BTrujillo816/coffee-scale/documentation/assets/HX711 Breakout rev A.png

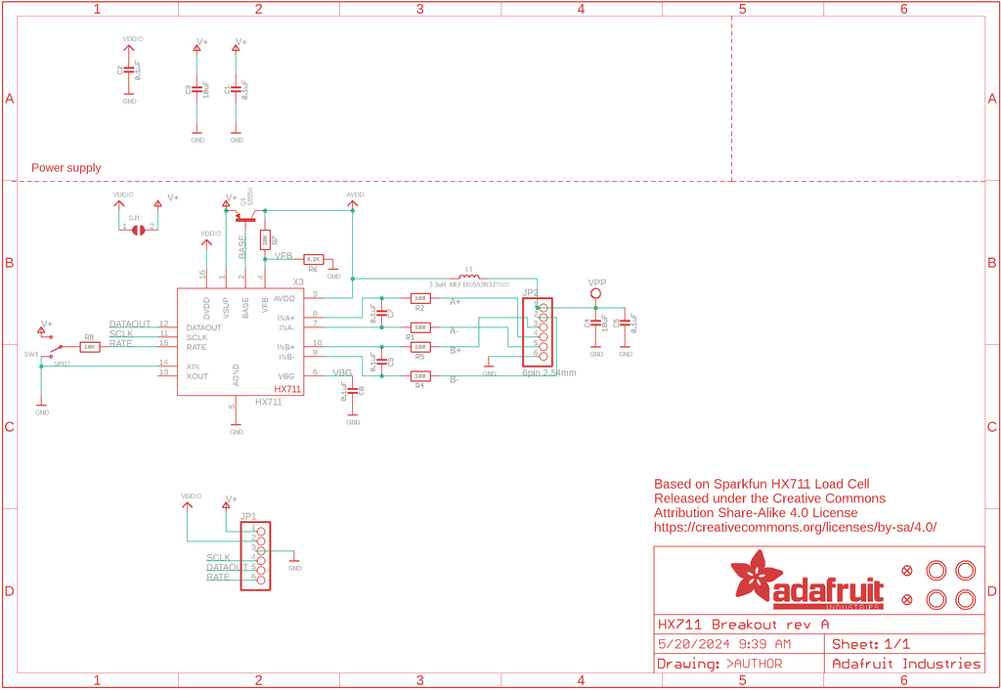
documentation/assets/HX711 Breakout rev A.png
