BTrujillo816/coffee-scale/documentation/TestDocument.assets/Current_prototype_11-13-24.jpg

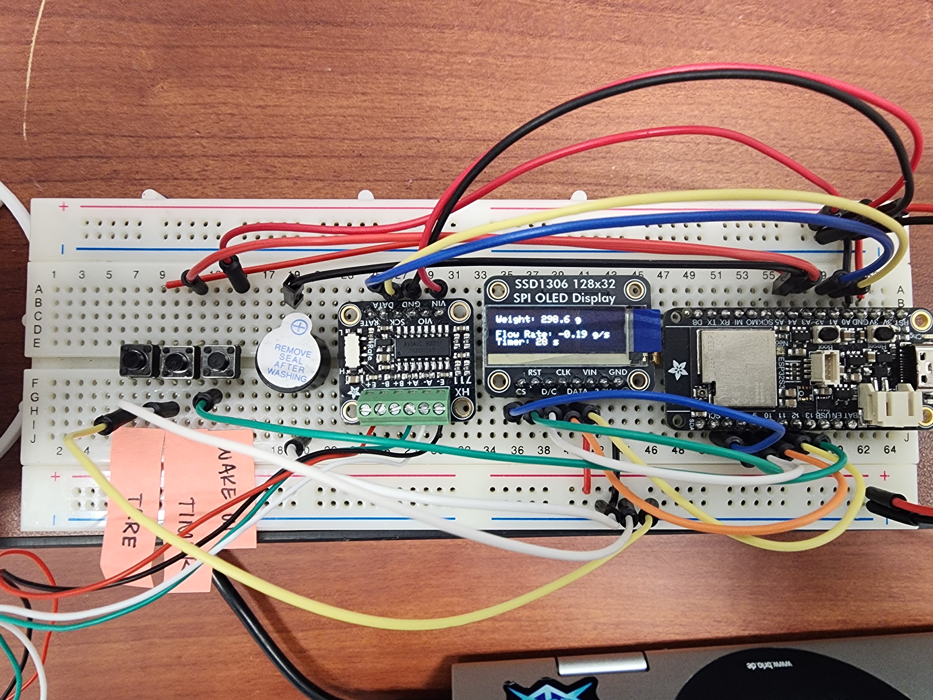
documentation/TestDocument.assets/Current_prototype_11-13-24.jpg
