BTrujillo816/coffee-scale/documentation/TestDocument.assets/Large_weight_test_control.jpg

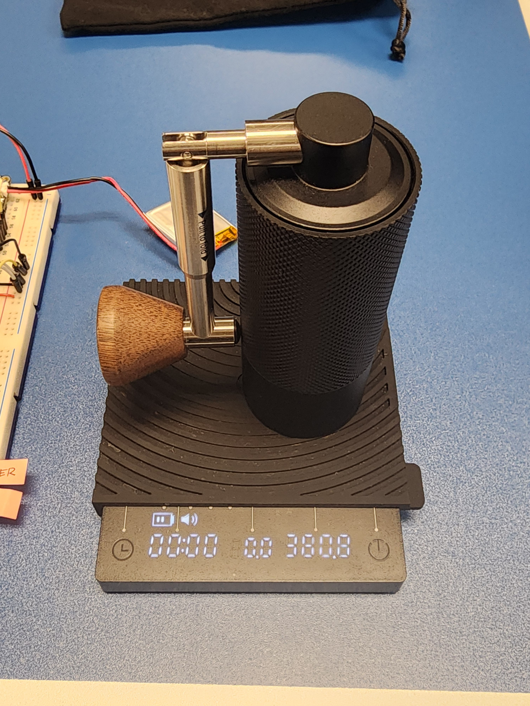
documentation/TestDocument.assets/Large_weight_test_control.jpg
