BTrujillo816/coffee-scale/documentation/Tests-BrandonTrujillo.assets/Types-of-Performance-testing-1024.webp

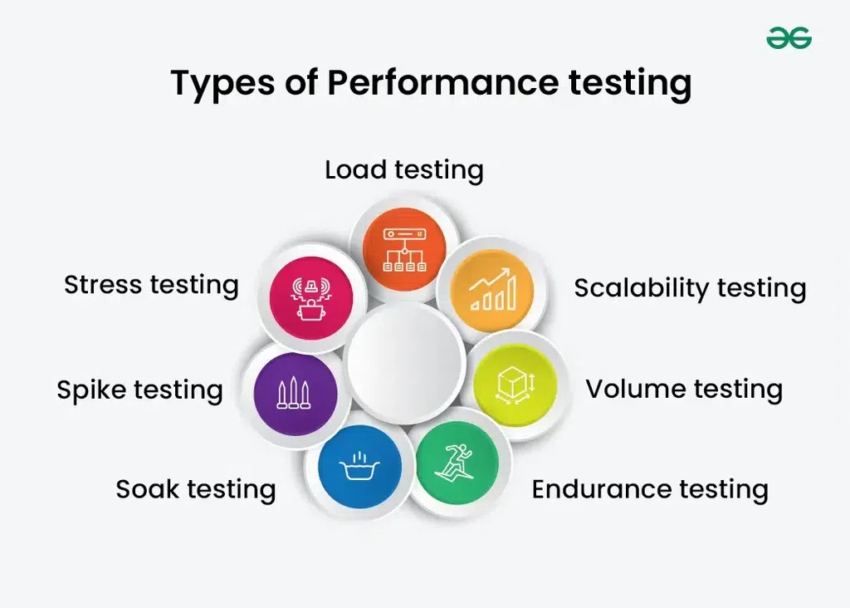
documentation/Tests-BrandonTrujillo.assets/Types-of-Performance-testing-1024.webp
