BTrujillo816/coffee-scale/logbook/10-30-24.assets/Result_LoadCell_Test.png

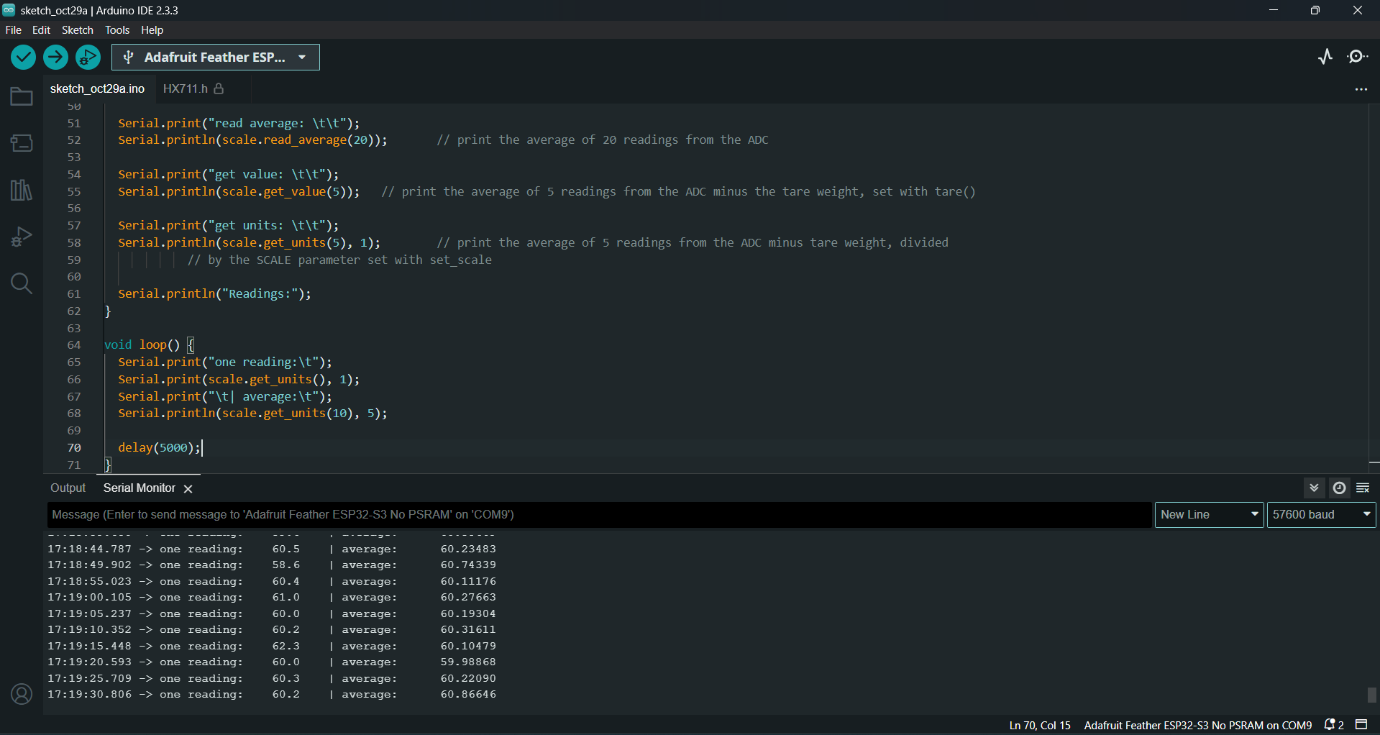
logbook/10-30-24.assets/Result_LoadCell_Test.png
