BTrujillo816/coffee-scale/logbook/10-30-24.assets/Result_Oled_Test_on_ESP32.jpg

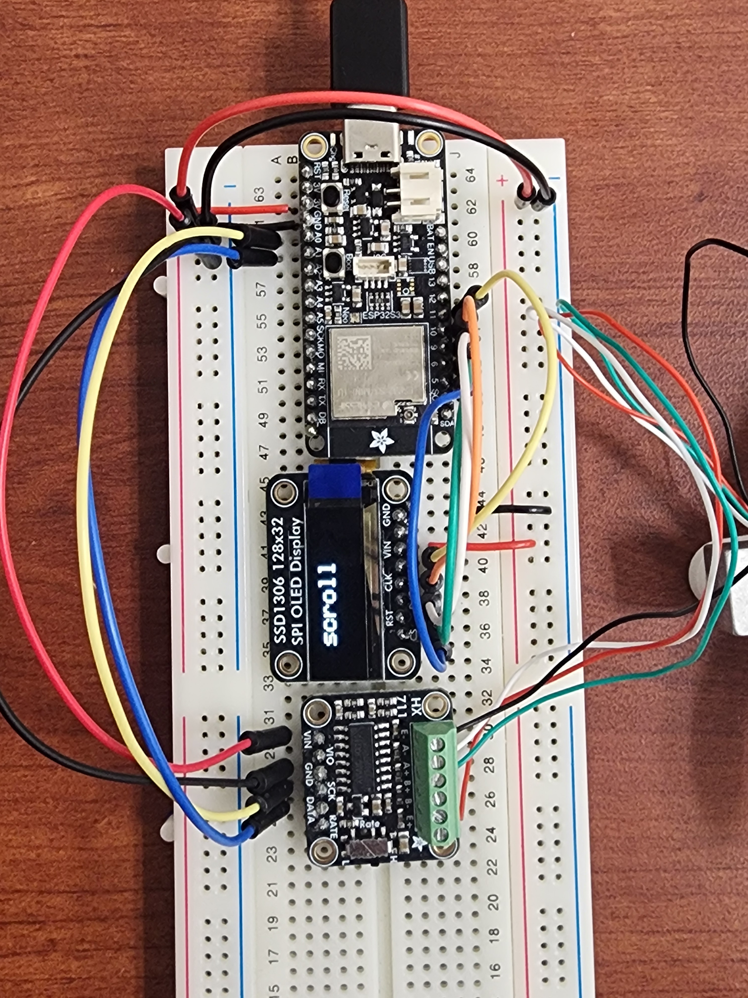
logbook/10-30-24.assets/Result_Oled_Test_on_ESP32.jpg
