BTrujillo816/coffee-scale/logbook/10-30-24.assets/Test_Weight.jpg

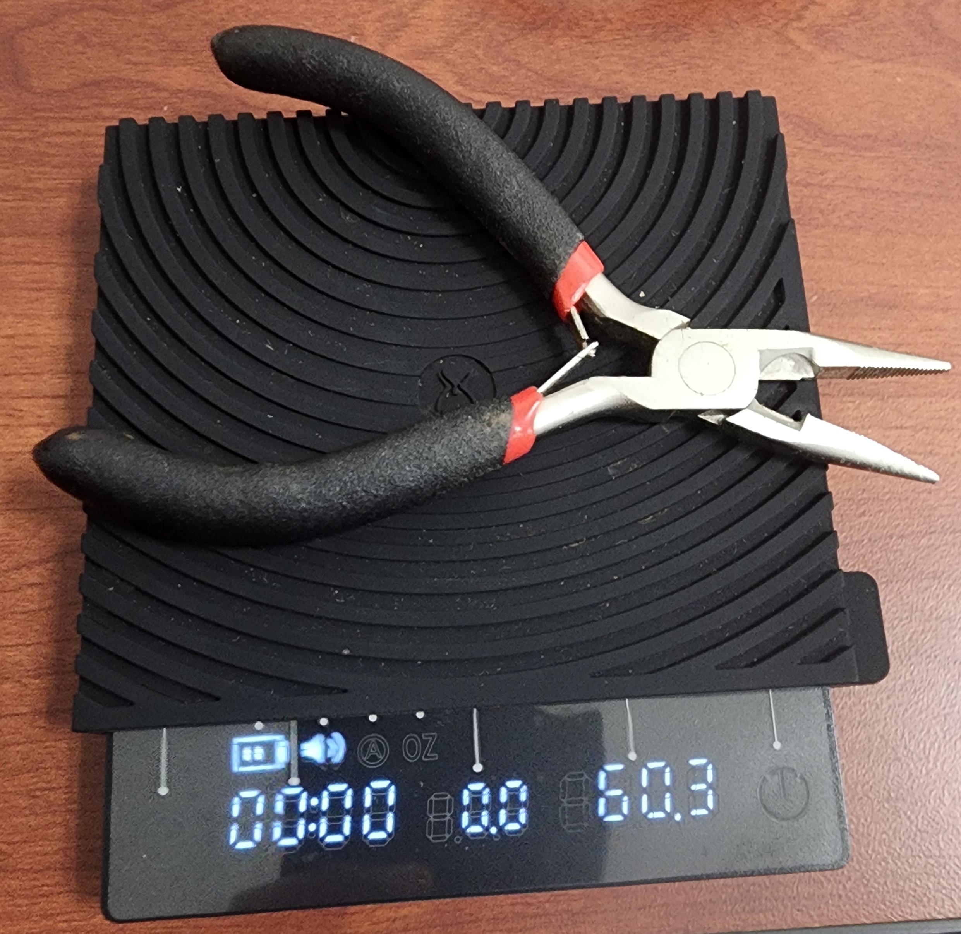
logbook/10-30-24.assets/Test_Weight.jpg
