BTrujillo816/coffee-scale/logbook/10-08-24.assets/image-20241016150546081.png

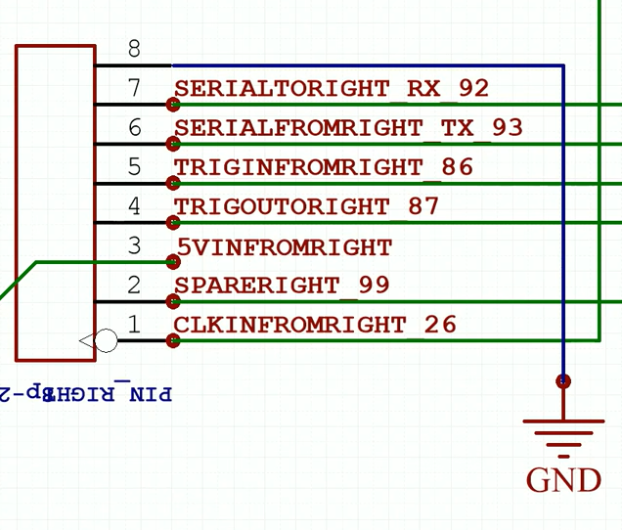
logbook/10-08-24.assets/image-20241016150546081.png
