BTrujillo816/coffee-scale/logbook/10-08-24.assets/image-20241016151650485.png

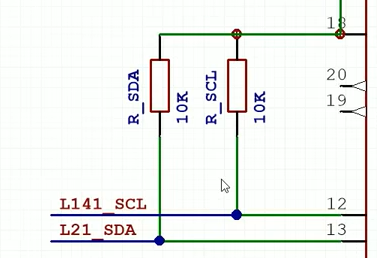
logbook/10-08-24.assets/image-20241016151650485.png
