BTrujillo816/coffee-scale/documentation/TestDocument.assets/Small_weight_test_control.jpg

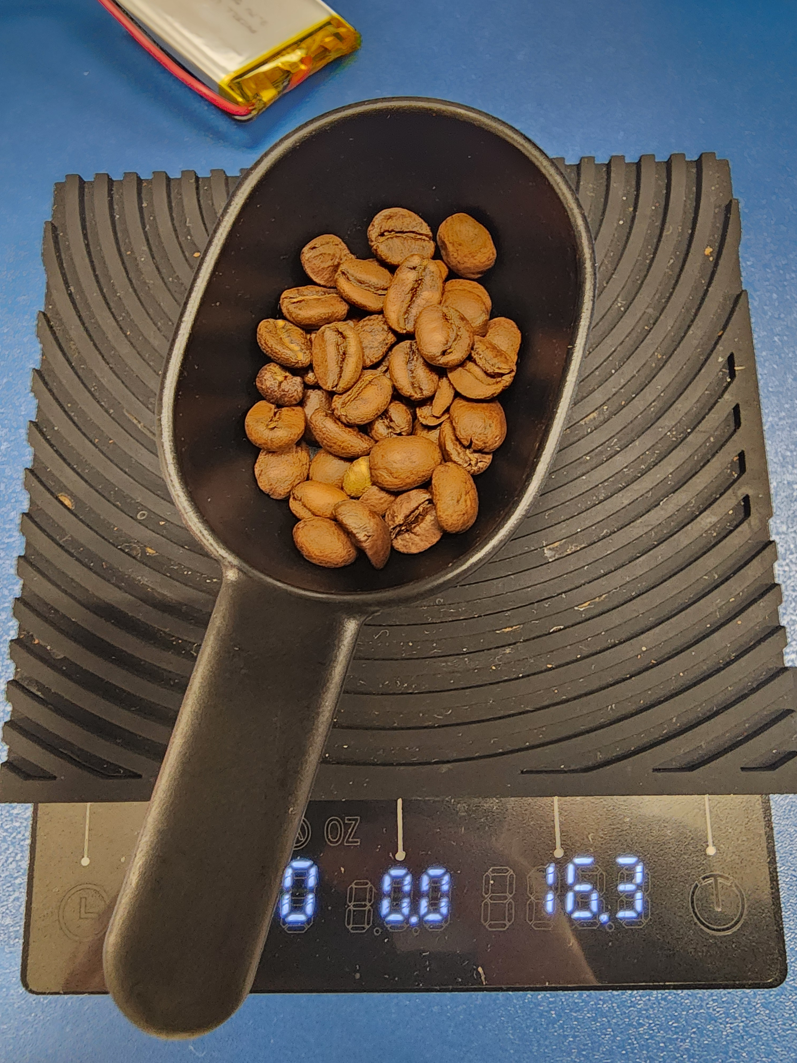
documentation/TestDocument.assets/Small_weight_test_control.jpg
